aemcee/Wireless-Toy-Project/Software/Function_Test_Code/ultrasonicSensor_The_Unit_Test/ultrasonicSensor_The_Unit_Test.ino

const int pingPin = 2; // Trigger Pin of Ultrasonic Sensor on The Unit
const int echoPin = 4; // Echo Pin of Ultrasonic Sensor on The Unit

void setup() {
   Serial.begin(9600); // Starting Serial Terminal
}

void loop() {
   long duration, inches, cm;
   pinMode(pingPin, OUTPUT);
   digitalWrite(pingPin, LOW);
   delayMicroseconds(2);
   digitalWrite(pingPin, HIGH);
   delayMicroseconds(10);
   digitalWrite(pingPin, LOW);
   pinMode(echoPin, INPUT);
   duration = pulseIn(echoPin, HIGH);
   inches = microsecondsToInches(duration);
   cm = microsecondsToCentimeters(duration);

   if(inches < 4){
    Serial.print("ayy you're close");
   };
   Serial.print(inches);
//   Serial.print("in, ");
//   Serial.print(cm);
//   Serial.print("cm");
   Serial.println();
   delay(100);
}

long microsecondsToInches(long microseconds) {
   return microseconds / 74 / 2;
}

long microsecondsToCentimeters(long microseconds) {
   return microseconds / 29 / 2;
}
